GreyPouponDijon/Bachelor-Project/03. NordicWings/Cockpit.c

// Generated using GB Export by AngelSix https://github.com/angelsix/retrosix-resources
// Enhanced version based of original by https://github.com/gabrielcnr

const unsigned char Cockpit_tileset[] = {

	// Tile 1
	0x00, 0x00, 0x00, 0x00, 0x00, 0x00, 0x00, 0x00, 0x00, 0x00, 0x00, 0x00, 0x00, 0x00, 0x00, 0x00, 
	// Tile 2
	0x00, 0x00, 0x00, 0x00, 0x00, 0x00, 0x00, 0x00, 0x00, 0x00, 0x00, 0x00, 0x00, 0x00, 0x01, 0x01, 
	// Tile 3
	0x0f, 0x0f, 0x70, 0x7f, 0x80, 0xff, 0x0f, 0xf0, 0x7f, 0x80, 0xff, 0x00, 0xff, 0x1f, 0xf0, 0x1f, 
	// Tile 4
	0x0e, 0x0f, 0x70, 0x7f, 0x81, 0xfe, 0x0f, 0xf0, 0x7f, 0x80, 0xff, 0x00, 0xff, 0x00, 0xff, 0x00, 
	// Tile 5
	0xf0, 0xf0, 0x0e, 0xfe, 0x01, 0xff, 0xf0, 0x0f, 0xfe, 0x01, 0xff, 0x00, 0xff, 0x80, 0xff, 0x40, 
	// Tile 6
	0x00, 0x00, 0x00, 0x00, 0x00, 0x00, 0x00, 0x00, 0x00, 0x00, 0x00, 0x00, 0x00, 0x00, 0x80, 0x80, 
	// Tile 7
	0x70, 0xf0, 0x0e, 0xfe, 0x81, 0x7f, 0xf0, 0x0f, 0xfe, 0x01, 0xff, 0x00, 0xff, 0x00, 0xff, 0x00, 
	// Tile 8
	0xff, 0x00, 0xff, 0x00, 0xff, 0x00, 0xff, 0x00, 0xff, 0x00, 0xff, 0x00, 0xff, 0x00, 0xff, 0x00, 
	// Tile 9
	0x00, 0x00, 0x00, 0x00, 0x00, 0x00, 0x00, 0x00, 0x00, 0x00, 0x07, 0x07, 0x38, 0x3f, 0xc0, 0xff, 
	// Tile 10
	0x00, 0x00, 0x00, 0x00, 0x03, 0x03, 0x1c, 0x1f, 0xe0, 0xff, 0x03, 0xfc, 0x1f, 0xe0, 0xff, 0x00, 
	// Tile 11
	0x07, 0xf8, 0x3f, 0xc0, 0xff, 0x00, 0xff, 0x00, 0xff, 0x00, 0xff, 0x00, 0xfe, 0x01, 0xf1, 0x0e, 
	// Tile 12
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

};
