GreyPouponDijon/Bachelor-Project/03. NordicWings/Splashscreen.c

// Generated using GB Export by AngelSix https://github.com/angelsix/retrosix-resources
// Enhanced version based of original by https://github.com/gabrielcnr

const unsigned char Splashscreen_tileset[] = {

	// Tile 1
	0x00, 0x00, 0x00, 0x00, 0x00, 0x00, 0x00, 0x00, 0x00, 0x00, 0x00, 0x00, 0x00, 0x00, 0x00, 0x00, 
	// Tile 2
	0x00, 0x01, 0x01, 0x02, 0x01, 0x02, 0x00, 0x01, 0x00, 0x00, 0x00, 0x01, 0x00, 0x01, 0x00, 0x00, 
	// Tile 3
	0x00, 0xf8, 0x08, 0x07, 0x01, 0x00, 0x80, 0x00, 0x00, 0xc0, 0x80, 0x30, 0x84, 0x08, 0x43, 0x80, 
	// Tile 4
	0x00, 0x00, 0x00, 0x00, 0x00, 0xf0, 0x10, 0x0f, 0x03, 0x00, 0x00, 0x00, 0x00, 0x00, 0x00, 0x00, 
	// Tile 5
	0x00, 0x00, 0x00, 0x00, 0x00, 0x00, 0x00, 0x00, 0x00, 0x80, 0x00, 0x40, 0x00, 0x20, 0x00, 0x20, 
	// Tile 6
	0x00, 0x00, 0x00, 0x00, 0x00, 0x00, 0x00, 0x00, 0x00, 0x00, 0x00, 0x03, 0x00, 0x0f, 0x10, 0x0f, 
	// Tile 7
	0x00, 0x00, 0x00, 0x00, 0x00, 0x0c, 0x00, 0x3f, 0x00, 0xff, 0x00, 0xff, 0x00, 0xff, 0x00, 0xff, 
	// Tile 8
	0x00, 0x00, 0x00, 0x00, 0x00, 0x00, 0x00, 0x00, 0x00, 0xc0, 0x00, 0xf0, 0x00, 0xfc, 0x00, 0xff, 
	// Tile 9
	0x00, 0x00, 0x00, 0x00, 0x00, 0x00, 0x03, 0x00, 0x0f, 0x00, 0x3f, 0x00, 0xff, 0x00, 0xff, 0x00, 
	// Tile 10
	0x00, 0x00, 0x00, 0x00, 0x80, 0x60, 0x80, 0x78, 0x80, 0x7e, 0x80, 0x7f, 0x80, 0x7f, 0x80, 0x7f, 
	// Tile 11
	0x00, 0x00, 0x00, 0x00, 0x00, 0x00, 0x00, 0x00, 0x00, 0x00, 0x00, 0x80, 0x00, 0xe0, 0x00, 0xf0, 
	// Tile 12
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

};
