GreyPouponDijon/Bachelor-Project/03. NordicWings/Rings.c

// Generated using GB Export by AngelSix https://github.com/angelsix/retrosix-resources
// Enhanced version based of original by https://github.com/gabrielcnr

const unsigned char Rings_tileset[] = {

	// Tile 1
	0x00, 0x00, 0x00, 0x00, 0x00, 0x00, 0x00, 0x00, 0x00, 0x00, 0x00, 0x00, 0x00, 0x00, 0x00, 0x00, 
	// Tile 2
	0x00, 0x00, 0x00, 0x00, 0x00, 0x00, 0x00, 0x00, 0x00, 0x00, 0x00, 0x00, 0x00, 0x03, 0x00, 0x02, 
	// Tile 3
	0x00, 0x00, 0x00, 0x00, 0x00, 0x00, 0x00, 0x00, 0x00, 0x00, 0x00, 0x00, 0x00, 0xc0, 0x00, 0x40, 
	// Tile 4
	0x00, 0x02, 0x00, 0x03, 0x00, 0x00, 0x00, 0x00, 0x00, 0x00, 0x00, 0x00, 0x00, 0x00, 0x00, 0x00, 
	// Tile 5
	0x00, 0x40, 0x00, 0xc0, 0x00, 0x00, 0x00, 0x00, 0x00, 0x00, 0x00, 0x00, 0x00, 0x00, 0x00, 0x00, 
	// Tile 6
	0x00, 0x00, 0x00, 0x00, 0x00, 0x00, 0x00, 0x00, 0x00, 0x0f, 0x00, 0x08, 0x00, 0x08, 0x00, 0x08, 
	// Tile 7
	0x00, 0x00, 0x00, 0x00, 0x00, 0x00, 0x00, 0x00, 0x00, 0xf0, 0x00, 0x10, 0x00, 0x10, 0x00, 0x10, 
	// Tile 8
	0x00, 0x08, 0x00, 0x08, 0x00, 0x08, 0x00, 0x0f, 0x00, 0x00, 0x00, 0x00, 0x00, 0x00, 0x00, 0x00, 
	// Tile 9
	0x00, 0x10, 0x00, 0x10, 0x00, 0x10, 0x00, 0xf0, 0x00, 0x00, 0x00, 0x00, 0x00, 0x00, 0x00, 0x00, 
	// Tile 10
	0x00, 0x00, 0x00, 0x7f, 0x00, 0x40, 0x00, 0x40, 0x00, 0x40, 0x00, 0x40, 0x00, 0x40, 0x00, 0x40, 
	// Tile 11
	0x00, 0x00, 0x00, 0xfe, 0x00, 0x02, 0x00, 0x02, 0x00, 0x02, 0x00, 0x02, 0x00, 0x02, 0x00, 0x02, 
	// Tile 12
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

};
