GreyPouponDijon/Bachelor-Project/03. NordicWings/Numbers.c

// Generated using GB Export by AngelSix https://github.com/angelsix/retrosix-resources
// Enhanced version based of original by https://github.com/gabrielcnr

const unsigned char Numbers_tileset[] = {

	// Tile 1
	0x00, 0x00, 0x00, 0x00, 0x00, 0x00, 0x00, 0x00, 0x00, 0x00, 0x00, 0x00, 0x00, 0x00, 0x00, 0x00, 
	// Tile 2
	0x00, 0x00, 0x18, 0x18, 0x24, 0x24, 0x24, 0x24, 0x24, 0x24, 0x24, 0x24, 0x18, 0x18, 0x00, 0x00, 
	// Tile 3
	0x00, 0x00, 0x18, 0x18, 0x08, 0x08, 0x08, 0x08, 0x08, 0x08, 0x08, 0x08, 0x08, 0x08, 0x00, 0x00, 
	// Tile 4
	0x00, 0x00, 0x18, 0x18, 0x24, 0x24, 0x04, 0x04, 0x08, 0x08, 0x10, 0x10, 0x3c, 0x3c, 0x00, 0x00, 
	// Tile 5
	0x00, 0x00, 0x18, 0x18, 0x24, 0x24, 0x08, 0x08, 0x04, 0x04, 0x24, 0x24, 0x18, 0x18, 0x00, 0x00, 
	// Tile 6
	0x00, 0x00, 0x24, 0x24, 0x24, 0x24, 0x3c, 0x3c, 0x04, 0x04, 0x04, 0x04, 0x04, 0x04, 0x00, 0x00, 
	// Tile 7
	0x00, 0x00, 0x3c, 0x3c, 0x20, 0x20, 0x38, 0x38, 0x04, 0x04, 0x04, 0x04, 0x38, 0x38, 0x00, 0x00, 
	// Tile 8
	0x00, 0x00, 0x18, 0x18, 0x20, 0x20, 0x38, 0x38, 0x24, 0x24, 0x24, 0x24, 0x18, 0x18, 0x00, 0x00, 
	// Tile 9
	0x00, 0x00, 0x3c, 0x3c, 0x04, 0x04, 0x08, 0x08, 0x08, 0x08, 0x10, 0x10, 0x10, 0x10, 0x00, 0x00, 
	// Tile 10
	0x00, 0x00, 0x18, 0x18, 0x24, 0x24, 0x18, 0x18, 0x24, 0x24, 0x24, 0x24, 0x18, 0x18, 0x00, 0x00, 
	// Tile 11
	0x00, 0x00, 0x18, 0x18, 0x24, 0x24, 0x24, 0x24, 0x1c, 0x1c, 0x04, 0x04, 0x18, 0x18, 0x00, 0x00, 
	// Tile 12
	0x00, 0x00, 0x00, 0x00, 0x06, 0x06, 0x08, 0x08, 0x04, 0x04, 0x02, 0x02, 0x0c, 0x0c, 0x00, 0x00, 
	// Tile 13
	0x00, 0x00, 0x00, 0x00, 0x66, 0x66, 0x89, 0x89, 0x89, 0x89, 0x89, 0x89, 0x66, 0x66, 0x00, 0x00, 
	// Tile 14
	0x00, 0x00, 0x00, 0x00, 0x67, 0x67, 0x54, 0x54, 0x66, 0x66, 0x54, 0x54, 0x57, 0x57, 0x00, 0x00, 
	// Tile 15
	0x00, 0x00, 0x00, 0x00, 0xce, 0xce, 0xa8, 0xa8, 0xcc, 0xcc, 0x88, 0x88, 0x8e, 0x8e, 0x00, 0x00, 
	// Tile 16
	0x00, 0x00, 0x00, 0x00, 0xec, 0xec, 0x8a, 0x8a, 0xca, 0xca, 0x8a, 0x8a, 0xec, 0xec, 0x00, 0x00, 

}; 
 
const unsigned char Numbers_tilemap[] = {

	// Frame 1
	0x01, 

	// Frame 2
	0x02, 

	// Frame 3
	0x03, 

	// Frame 4
	0x04, 

	// Frame 5
	0x05, 

	// Frame 6
	0x06, 

	// Frame 7
	0x07, 

	// Frame 8
	0x08, 

	// Frame 9
	0x09, 

	// Frame 10
	0x0a, 

	// Frame 11
	0x0b, 

	// Frame 12
	0x0c, 

	// Frame 13
	0x0d, 

	// Frame 14
	0x0e, 

	// Frame 15
	0x0f, 

};
